masneyb/weather-station/pi-yadl/src/sensor_bme280.c

/*
 * The BME280 driver was originally downloaded from
 * https://github.com/masneyb/raspberry-pi-bme280
 *
 * Modified BSD License
 * ====================
 *
 * Copyright © 2016, Andrei Vainik
 * Copyright © 2016-2017 Brian Masney
 * All rights reserved.
 *
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
 * 1. Redistributions of source code must retain the above copyright
 *    notice, this list of conditions and the following disclaimer.
 * 2. Redistributions in binary form must reproduce the above copyright
 *    notice, this list of conditions and the following disclaimer in the
 *    documentation and/or other materials provided with the distribution.
 * 3. Neither the name of the organization nor the
 *    names of its contributors may be used to endorse or promote products
 *    derived from this software without specific prior written permission.
 *
 * THIS SOFTWARE IS PROVIDED BY THE COPYRIGHT HOLDERS AND CONTRIBUTORS "AS IS"
 * AND ANY EXPRESS OR IMPLIED WARRANTIES, INCLUDING, BUT NOT LIMITED TO, THE
 * IMPLIED WARRANTIES OF MERCHANTABILITY AND FITNESS FOR A PARTICULAR PURPOSE
 * ARE DISCLAIMED. IN NO EVENT SHALL COPYRIGHT HOLDER BE LIABLE FOR ANY
 * DIRECT, INDIRECT, INCIDENTAL, SPECIAL, EXEMPLARY, OR CONSEQUENTIAL DAMAGES
 * (INCLUDING, BUT NOT LIMITED TO, PROCUREMENT OF SUBSTITUTE GOODS OR SERVICES;
 * LOSS OF USE, DATA, OR PROFITS; OR BUSINESS INTERRUPTION) HOWEVER CAUSED AND
 * ON ANY THEORY OF LIABILITY, WHETHER IN CONTRACT, STRICT LIABILITY, OR TORT
 * (INCLUDING NEGLIGENCE OR OTHERWISE) ARISING IN ANY WAY OUT OF THE USE OF THIS
 * SOFTWARE, EVEN IF ADVISED OF THE POSSIBILITY OF SUCH DAMAGE.
 *
 * This piece of code was combined from several sources
 * https://github.com/adafruit/Adafruit_BME280_Library
 * https://cdn-shop.adafruit.com/datasheets/BST-BME280_DS001-10.pdf
 * https://projects.drogon.net/raspberry-pi/wiringpi/i2c-library/
 *
 *******************************************************************************
 *
 * This is a library for the BME280 humidity, temperature & pressure sensor
 *
 * Designed specifically to work with the Adafruit BME280 Breakout
 * ----> http://www.adafruit.com/products/2650
 *
 * These sensors use I2C or SPI to communicate, 2 or 4 pins are required
 * to interface.
 *
 * Adafruit invests time and resources providing this open source code,
 * please support Adafruit and open-source hardware by purchasing products
 * from Adafruit!
 *
 * Written by Limor Fried & Kevin Townsend for Adafruit Industries.
 * BSD license, all text above must be included in any redistribution
 */


#include <stdio.h>
#include <stdlib.h>
#include <errno.h>
#include <stdint.h>
#include <time.h>
#include <math.h>
#include <wiringPiI2C.h>
#include "yadl.h"

#define BME280_REGISTER_DIG_T1        0x88
#define BME280_REGISTER_DIG_T2        0x8A
#define BME280_REGISTER_DIG_T3        0x8C
#define BME280_REGISTER_DIG_P1        0x8E
#define BME280_REGISTER_DIG_P2        0x90
#define BME280_REGISTER_DIG_P3        0x92
#define BME280_REGISTER_DIG_P4        0x94
#define BME280_REGISTER_DIG_P5        0x96
#define BME280_REGISTER_DIG_P6        0x98
#define BME280_REGISTER_DIG_P7        0x9A
#define BME280_REGISTER_DIG_P8        0x9C
#define BME280_REGISTER_DIG_P9        0x9E
#define BME280_REGISTER_DIG_H1        0xA1
#define BME280_REGISTER_DIG_H2        0xE1
#define BME280_REGISTER_DIG_H3        0xE3
#define BME280_REGISTER_DIG_H4        0xE4
#define BME280_REGISTER_DIG_H5        0xE5
#define BME280_REGISTER_DIG_H6        0xE7
#define BME280_REGISTER_CHIPID        0xD0
#define BME280_REGISTER_VERSION       0xD1
#define BME280_REGISTER_SOFTRESET     0xE0
#define BME280_RESET                  0xB6
#define BME280_REGISTER_CAL26         0xE1
#define BME280_REGISTER_CONTROLHUMID  0xF2
#define BME280_REGISTER_CONTROL       0xF4
#define BME280_REGISTER_CONFIG        0xF5
#define BME280_REGISTER_PRESSUREDATA  0xF7
#define BME280_REGISTER_TEMPDATA      0xFA
#define BME280_REGISTER_HUMIDDATA     0xFD

#define MEAN_SEA_LEVEL_PRESSURE       1013

typedef struct {
	uint16_t dig_T1;
	int16_t  dig_T2;
	int16_t  dig_T3;

	uint16_t dig_P1;
	int16_t  dig_P2;
	int16_t  dig_P3;
	int16_t  dig_P4;
	int16_t  dig_P5;
	int16_t  dig_P6;
	int16_t  dig_P7;
	int16_t  dig_P8;
	int16_t  dig_P9;

	uint8_t  dig_H1;
	int16_t  dig_H2;
	uint8_t  dig_H3;
	int16_t  dig_H4;
	int16_t  dig_H5;
	int8_t   dig_H6;
} bme280_calib_data;

typedef struct {
	uint8_t pmsb;
	uint8_t plsb;
	uint8_t pxsb;

	uint8_t tmsb;
	uint8_t tlsb;
	uint8_t txsb;

	uint8_t hmsb;
	uint8_t hlsb;

	uint32_t temperature;
	uint32_t pressure;
	uint32_t humidity;

} bme280_raw_data;


static int32_t bme280_get_temperature_calibration(bme280_calib_data *cal,
						  uint32_t adc_T)
{
	int32_t var1  = ((((adc_T>>3) - ((int32_t)cal->dig_T1 << 1))) *
	   ((int32_t)cal->dig_T2)) >> 11;

	int32_t var2  = (((((adc_T>>4) - ((int32_t)cal->dig_T1)) *
	     ((adc_T>>4) - ((int32_t)cal->dig_T1))) >> 12) *
	   ((int32_t)cal->dig_T3)) >> 14;

	return var1 + var2;
}

static void bme280_read_calibration_data(int fd, bme280_calib_data *data)
{
	data->dig_T1 = (uint16_t) wiringPiI2CReadReg16(fd,
						       BME280_REGISTER_DIG_T1);
	data->dig_T2 = (int16_t) wiringPiI2CReadReg16(fd,
						      BME280_REGISTER_DIG_T2);
	data->dig_T3 = (int16_t) wiringPiI2CReadReg16(fd,
						      BME280_REGISTER_DIG_T3);

	data->dig_P1 = (uint16_t) wiringPiI2CReadReg16(fd,
						       BME280_REGISTER_DIG_P1);
	data->dig_P2 = (int16_t) wiringPiI2CReadReg16(fd,
						      BME280_REGISTER_DIG_P2);
	data->dig_P3 = (int16_t) wiringPiI2CReadReg16(fd,
						      BME280_REGISTER_DIG_P3);
	data->dig_P4 = (int16_t) wiringPiI2CReadReg16(fd,
						      BME280_REGISTER_DIG_P4);
	data->dig_P5 = (int16_t) wiringPiI2CReadReg16(fd,
						      BME280_REGISTER_DIG_P5);
	data->dig_P6 = (int16_t) wiringPiI2CReadReg16(fd,
						      BME280_REGISTER_DIG_P6);
	data->dig_P7 = (int16_t) wiringPiI2CReadReg16(fd,
						      BME280_REGISTER_DIG_P7);
	data->dig_P8 = (int16_t) wiringPiI2CReadReg16(fd,
						      BME280_REGISTER_DIG_P8);
	data->dig_P9 = (int16_t) wiringPiI2CReadReg16(fd,
						      BME280_REGISTER_DIG_P9);

	data->dig_H1 = (uint8_t) wiringPiI2CReadReg8(fd,
						     BME280_REGISTER_DIG_H1);
	data->dig_H2 = (int16_t) wiringPiI2CReadReg16(fd,
						      BME280_REGISTER_DIG_H2);
	data->dig_H3 = (uint8_t) wiringPiI2CReadReg8(fd,
						     BME280_REGISTER_DIG_H3);
	data->dig_H4 = (wiringPiI2CReadReg8(fd, BME280_REGISTER_DIG_H4) << 4) |
		(wiringPiI2CReadReg8(fd, BME280_REGISTER_DIG_H4+1) & 0xF);
	data->dig_H5 = (wiringPiI2CReadReg8(fd,
					    BME280_REGISTER_DIG_H5+1) << 4) |
		(wiringPiI2CReadReg8(fd, BME280_REGISTER_DIG_H5) >> 4);
	data->dig_H6 = (int8_t) wiringPiI2CReadReg8(fd, BME280_REGISTER_DIG_H6);
}

static float bme280_compensate_temperature(uint32_t t_fine)
{
	float T  = (t_fine * 5 + 128) >> 8;

	return T / 100;
}

static float bme280_compensate_pressure(uint32_t adc_P, bme280_calib_data *cal,
					uint32_t t_fine)
{
	int64_t var1, var2, p;

	var1 = ((int64_t)t_fine) - 128000;
	var2 = var1 * var1 * (int64_t)cal->dig_P6;
	var2 = var2 + ((var1*(int64_t)cal->dig_P5)<<17);
	var2 = var2 + (((int64_t)cal->dig_P4)<<35);
	var1 = ((var1 * var1 * (int64_t)cal->dig_P3)>>8) +
	  ((var1 * (int64_t)cal->dig_P2)<<12);
	var1 = (((((int64_t)1)<<47)+var1))*((int64_t)cal->dig_P1)>>33;

	if (var1 == 0)
		return 0;

	p = 1048576 - adc_P;
	p = (((p<<31) - var2)*3125) / var1;
	var1 = (((int64_t)cal->dig_P9) * (p>>13) * (p>>13)) >> 25;
	var2 = (((int64_t)cal->dig_P8) * p) >> 19;

	p = ((p + var1 + var2) >> 8) + (((int64_t)cal->dig_P7)<<4);
	return (float)p/256;
}

static float bme280_compensate_humidity(uint32_t adc_H, bme280_calib_data *cal,
					uint32_t t_fine)
{
	int32_t v_x1_u32r;

	v_x1_u32r = (t_fine - ((int32_t)76800));

	v_x1_u32r = (((((adc_H << 14) - (((int32_t)cal->dig_H4) << 20) -
	    (((int32_t)cal->dig_H5) * v_x1_u32r)) + ((int32_t)16384)) >> 15) *
	 (((((((v_x1_u32r * ((int32_t)cal->dig_H6)) >> 10) *
	(((v_x1_u32r * ((int32_t)cal->dig_H3)) >> 11) +
	 ((int32_t)32768))) >> 10) +
	    ((int32_t)2097152)) * ((int32_t)cal->dig_H2) + 8192) >> 14));

	v_x1_u32r = (v_x1_u32r - (((((v_x1_u32r >> 15) *
				     (v_x1_u32r >> 15)) >> 7) *
				   ((int32_t)cal->dig_H1)) >> 4));

	v_x1_u32r = (v_x1_u32r < 0) ? 0 : v_x1_u32r;
	v_x1_u32r = (v_x1_u32r > 419430400) ? 419430400 : v_x1_u32r;
	float h = (v_x1_u32r>>12);

	return  h / 1024.0;
}

static void bme280_get_raw_data(int fd, bme280_raw_data *raw)
{
	wiringPiI2CWrite(fd, 0xf7);

	raw->pmsb = wiringPiI2CRead(fd);
	raw->plsb = wiringPiI2CRead(fd);
	raw->pxsb = wiringPiI2CRead(fd);

	raw->tmsb = wiringPiI2CRead(fd);
	raw->tlsb = wiringPiI2CRead(fd);
	raw->txsb = wiringPiI2CRead(fd);

	raw->hmsb = wiringPiI2CRead(fd);
	raw->hlsb = wiringPiI2CRead(fd);

	raw->temperature = 0;
	raw->temperature = (raw->temperature | raw->tmsb) << 8;
	raw->temperature = (raw->temperature | raw->tlsb) << 8;
	raw->temperature = (raw->temperature | raw->txsb) >> 4;

	raw->pressure = 0;
	raw->pressure = (raw->pressure | raw->pmsb) << 8;
	raw->pressure = (raw->pressure | raw->plsb) << 8;
	raw->pressure = (raw->pressure | raw->pxsb) >> 4;

	raw->humidity = 0;
	raw->humidity = (raw->humidity | raw->hmsb) << 8;
	raw->humidity = (raw->humidity | raw->hlsb);
}

static float bme280_get_altitude(float pressure)
{
	/*
	 * Equation taken from BMP180 datasheet (page 16):
	 * http://www.adafruit.com/datasheets/BST-BMP180-DS000-09.pdf
	 *
	 * Note that using the equation from wikipedia can give bad results
	 * at high altitude.  See this thread for more information:
	 * http://forums.adafruit.com/viewtopic.php?f=22&t=58064
	 */

	return 44330.0 *
		(1.0 - pow(pressure / MEAN_SEA_LEVEL_PRESSURE, 0.190294957));
}

static void _bme280_init(yadl_config *config)
{
	if (config->temperature_converter == NULL) {
		fprintf(stderr,
			"You must specify the --temperature_unit argument\n");
		usage();
	} else if (config->i2c_address == -1) {
		fprintf(stderr,
			"You must specify the --i2c_address argument\n");
		usage();
	}

	config->fd = wiringPiI2CSetup(config->i2c_address);
	if (config->fd < 0) {
		fprintf(stderr, "i2c device not found at address %x\n",
			config->i2c_address);
		usage();
	}

}

static yadl_result *_bme280_read_data(yadl_config *config)
{
	bme280_calib_data cal;

	bme280_read_calibration_data(config->fd, &cal);

	// humidity oversampling x 1
	wiringPiI2CWriteReg8(config->fd, 0xf2, 0x01);

	// pressure and temperature oversampling x 1, mode normal
	wiringPiI2CWriteReg8(config->fd, 0xf4, 0x25);

	bme280_raw_data raw;

	bme280_get_raw_data(config->fd, &raw);

	uint32_t t_fine = bme280_get_temperature_calibration(&cal,
							     raw.temperature);
	float temperature = bme280_compensate_temperature(t_fine);
	float humidity = bme280_compensate_humidity(raw.humidity, &cal, t_fine);
	float pressure = bme280_compensate_pressure(raw.pressure, &cal,
						    t_fine) / 100;
	float altitude = bme280_get_altitude(pressure);

	yadl_result *result = malloc(sizeof(*result));

	result->value = malloc(sizeof(float) * 5);
	result->value[0] = config->temperature_converter(temperature);
	result->value[1] = humidity;
	result->value[2] = pressure;
	result->value[3] = pressure * 0.0295301;
	result->value[4] = altitude;

	result->unit = malloc(sizeof(char *) * 1);
	result->unit[0] = config->temperature_unit;

	return result;
}

static char *_bme280_value_header_names[] = {
	"temperature", "humidity", "pressure_millibars", "pressure_in",
	"altitude", NULL
};

static char **_bme280_get_value_header_names(__attribute__((__unused__))
					     yadl_config *config)
{
	return _bme280_value_header_names;
}

static char *_bme280_unit_header_names[] = { "temperature_unit", NULL };

static char **_bme280_get_unit_header_names(__attribute__((__unused__))
					    yadl_config *config)
{
	return _bme280_unit_header_names;
}

sensor bme280_sensor_funcs = {
	.init = &_bme280_init,
	.get_value_header_names = &_bme280_get_value_header_names,
	.get_unit_header_names = &_bme280_get_unit_header_names,
	.read = _bme280_read_data


};
