masneyb/weather-station/pi-yadl/src/yadl.h

/*
 * yadl.h
 *
 * Copyright (C) 2016-2017 Brian Masney <masneyb@onstation.org>
 *
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
 * You should have received a copy of the GNU General Public License
 * along with this program; if not, write to the Free Software
 * Foundation, Inc., 51 Franklin Street, Fifth Floor, Boston, MA
 * 02110-1301, USA.
 */

#include <stdio.h>
#include "float_list.h"
#include "loggers.h"

typedef struct yadl_result_tag {
	float *value;
	char **unit;
} yadl_result;

typedef struct yadl_config_tag yadl_config;

typedef struct adc_converter_tag {
	void (*adc_init)(yadl_config *config);
	int (*adc_read)(yadl_config *config);
	int adc_resolution;
} adc_converter;

typedef struct output_metadata_tag {
	FILE *fd;
	char *outfile;
} output_metadata;

typedef struct outputter_tag {
	output_metadata *(*open)(yadl_config *config, char *outfile);
	void (*write_header)(output_metadata *meta, yadl_config *config);
	void (*write_result)(output_metadata *meta, int reading_number,
			     yadl_result *result, yadl_config *config);
	void (*write_footer)(output_metadata *meta);
	void (*close)(output_metadata *meta, yadl_config *config);
} outputter;

typedef struct sensor_tag {
	void (*init)(yadl_config *config);
	yadl_result * (*read)(yadl_config *config);
	char ** (*get_value_header_names)(yadl_config *config);
	char ** (*get_unit_header_names)(yadl_config *config);
} sensor;

typedef float (*filter)(float_node *list);

typedef float (*temperature_unit_converter)(float input);

#define NUM_WIND_2_MIN_SAMPLES   120
#define NUM_WIND_10_MIN_SAMPLES  600
#define NUM_WIND_60_MIN_SAMPLES 3600

struct yadl_config_tag {
	sensor *sens;
	int gpio_pin;
	logger logger;
	int spi_channel;
	int i2c_address;
	int analog_channel;
	adc_converter *adc;
	int sleep_millis_between_retries;
	int sleep_millis_between_results;
	int sleep_millis_between_samples;
	int max_retries;
	filter filter_func;
	int num_results;
	int num_samples_per_result;
	int remove_n_samples_from_ends;
	int only_log_value_changes;
	float *last_values;
	float counter_multiplier;
	char *interrupt_edge;
	int adc_millivolts;
	float adc_multiplier;
	char *temperature_unit;
	temperature_unit_converter temperature_converter;
	char *w1_slave;
	int analog_scaling_factor;
	int wind_speed_pin;
	int rain_gauge_pin;

	char *wind_speed_unit;
	float wind_speed_multiplier;

	char *rain_gauge_unit;
	float rain_gauge_multiplier;

	float_node *rain_gauge_1h;
	int num_rain_gauge_1h_samples;

	float_node *rain_gauge_6h;
	int num_rain_gauge_6h_samples;

	float_node *rain_gauge_24h;
	int num_rain_gauge_24h_samples;

	/**
	 * Keep track of the amount of rain that was seen since midnight
	 * local time
	 */
	int current_hour;
	int num_rain_clicks_today;

	/* Ring buffers for the historical wind data */
	float wind_directions_2m[NUM_WIND_2_MIN_SAMPLES];
	float wind_speeds_2m[NUM_WIND_2_MIN_SAMPLES];
	int wind_2m_idx;

	float wind_directions_10m[NUM_WIND_10_MIN_SAMPLES];
	float wind_speeds_10m[NUM_WIND_10_MIN_SAMPLES];
	int wind_10m_idx;

	float wind_directions_60m[NUM_WIND_60_MIN_SAMPLES];
	float wind_speeds_60m[NUM_WIND_60_MIN_SAMPLES];
	int wind_60m_idx;

	int fd;
};

filter get_filter(char *name);

outputter *get_outputter(char *name);

sensor bmp180_sensor_funcs;

sensor bme280_sensor_funcs;

sensor analog_sensor_funcs;

sensor argent_80422_sensor_funcs;

sensor digital_sensor_funcs;

sensor digital_counter_sensor_funcs;

sensor dht11_sensor_funcs;

sensor dht22_sensor_funcs;

sensor ds18b20_sensor_funcs;

sensor tmp36_sensor_funcs;

sensor *get_sensor(char *name);

adc_converter mcp3002_funcs;

adc_converter mcp3004_funcs;

adc_converter pcf8591_funcs;

adc_converter *get_adc(char *name);

void usage(void);

int get_num_values(yadl_config *config);

void populate_temperature_converter(yadl_config *config, char *name);
